cristinacolpos/PELA-blocks/motor/PELA-round-motor-enclosure.stl

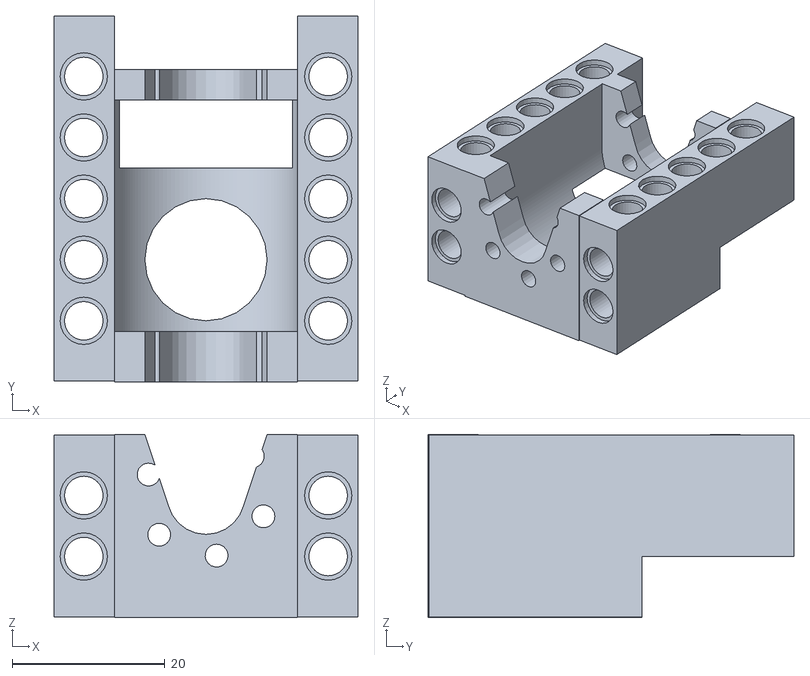
[picture p65: CAD file, 2020-01-09]
motor/PELA-round-motor-enclosure.stl
39.8 x 47.9 x 24.0
