cristinacolpos/PELA-blocks/peg/PELA-simplified-technic-peg-flexmaterial.stl

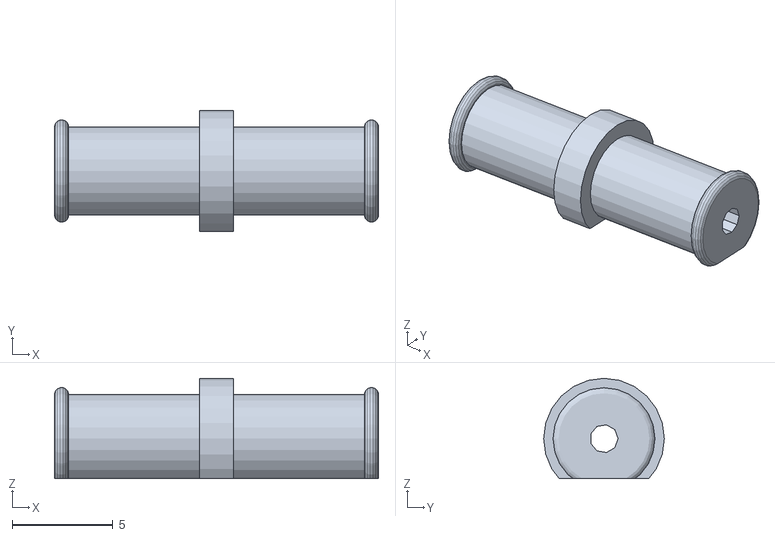
[picture p66: CAD file, 2020-01-09]
peg/PELA-simplified-technic-peg-flexmaterial.stl
16.1 x 6.00 x 4.99
