cristinacolpos/PELA-blocks/PELA-technic-block.stl

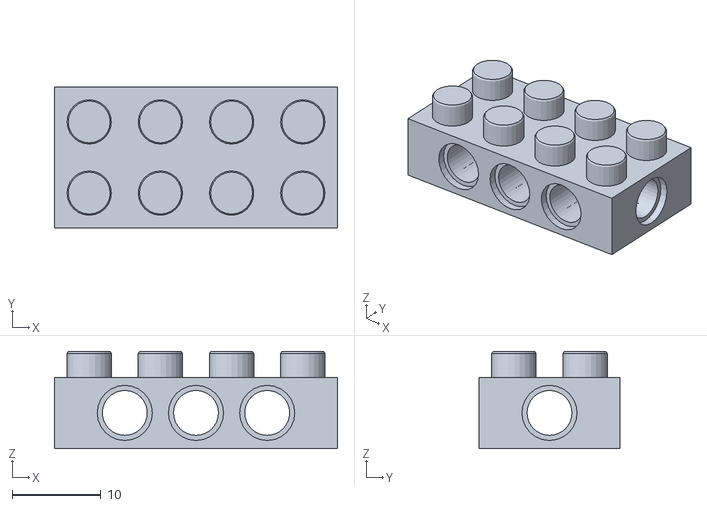
[picture p67: CAD file, 2020-01-09]
PELA-technic-block.stl
31.8 x 15.8 x 10.9
