cristinacolpos/PELA-blocks/sign/PELA-panel-sign.stl

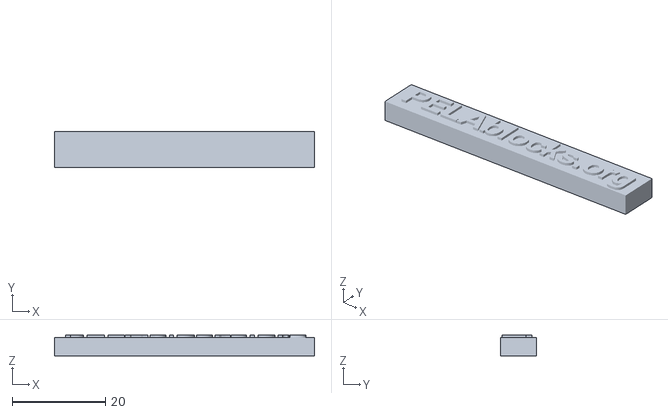
[picture p68: CAD file, 2019-11-25]
sign/PELA-panel-sign.stl
55.8 x 7.80 x 4.50
