cristinacolpos/PELA-blocks/technic-beam/PELA-technic-rail.stl

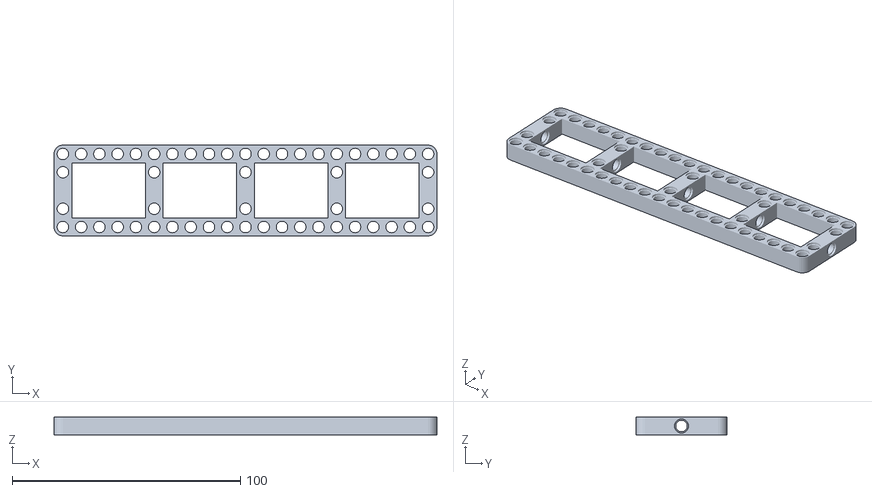
[picture p69: CAD file, 2020-01-09]
technic-beam/PELA-technic-rail.stl
167.8 x 39.8 x 7.80
