cristinacolpos/PELA-blocks/technic-mount/PELA-raspberry-pi-camera-technic-mount.stl

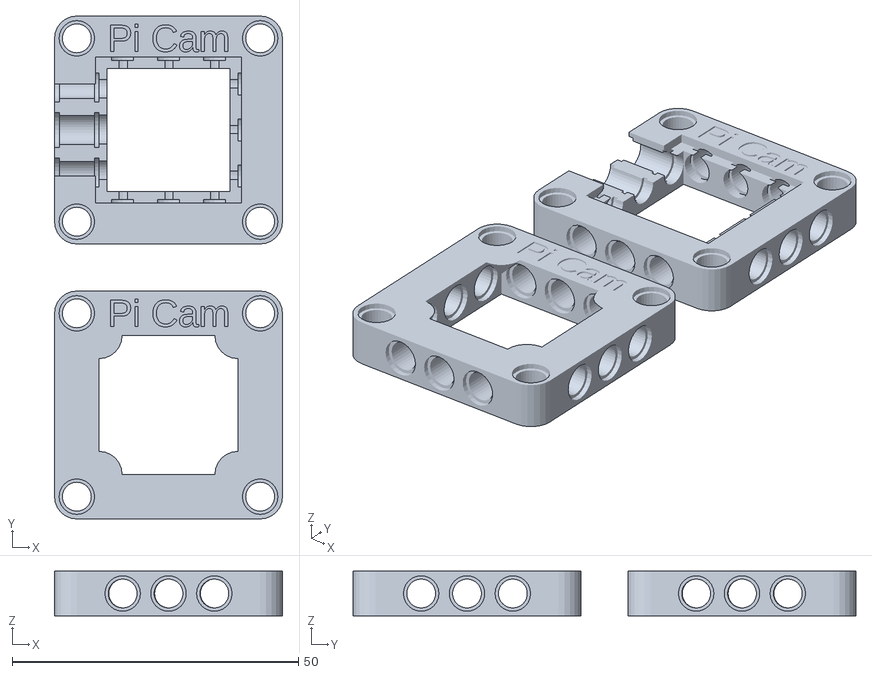
[picture p70: CAD file, 2020-01-09]
technic-mount/PELA-raspberry-pi-camera-technic-mount.stl
39.8 x 87.8 x 7.80
