cristinacolpos/PELA-blocks/axle/PELA-technic-axle.stl

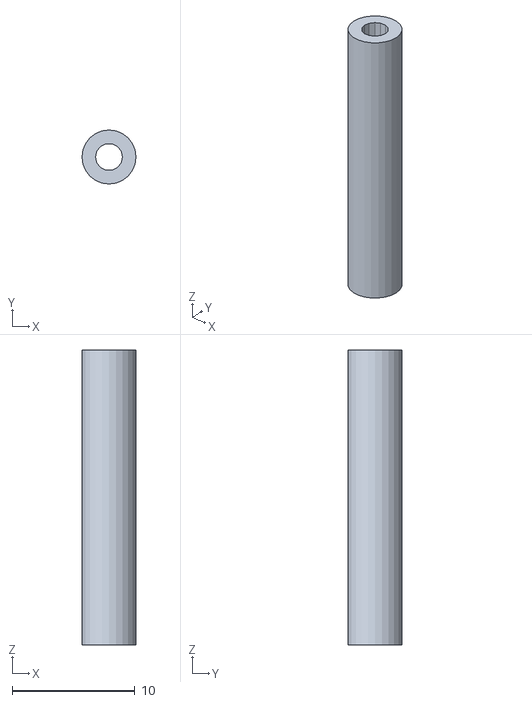
[picture p71: CAD file, 2019-11-25]
axle/PELA-technic-axle.stl
4.40 x 4.40 x 24.0
