cristinacolpos/PELA-blocks/peg/PELA-technic-peg.stl

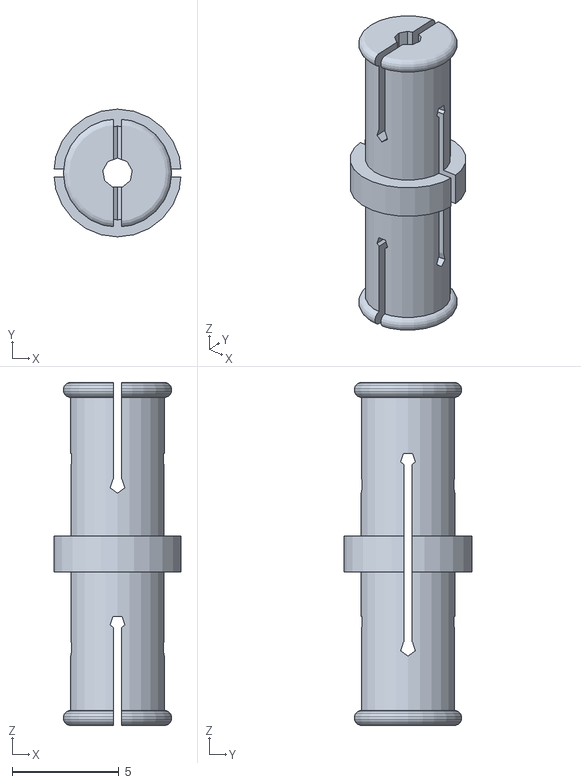
[picture p72: CAD file, 2020-01-09]
peg/PELA-technic-peg.stl
5.95 x 6.00 x 16.1
