cristinacolpos/PELA-blocks/PELA-strap-mount.stl

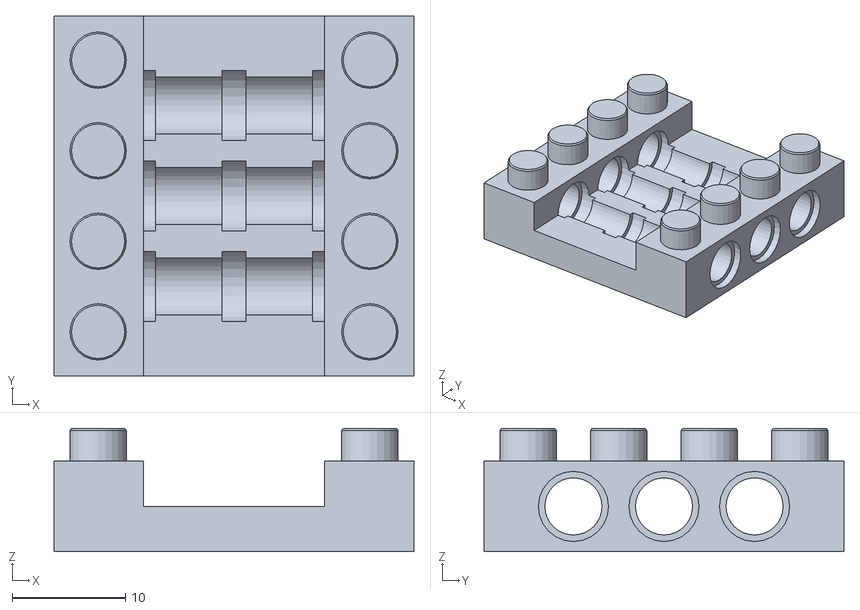
[picture p73: CAD file, 2020-01-09]
PELA-strap-mount.stl
31.8 x 31.8 x 10.9
