cristinacolpos/PELA-blocks/technic-beam/PELA-technic-twist-beam.stl

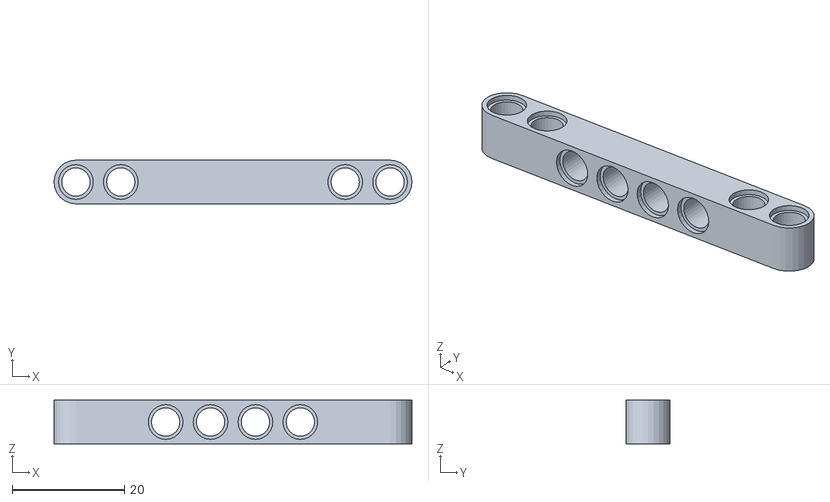
[picture p74: CAD file, 2020-01-09]
technic-beam/PELA-technic-twist-beam.stl
63.8 x 7.80 x 7.80
