cristinacolpos/PELA-blocks/technic-beam/PELA-technic-beam.stl

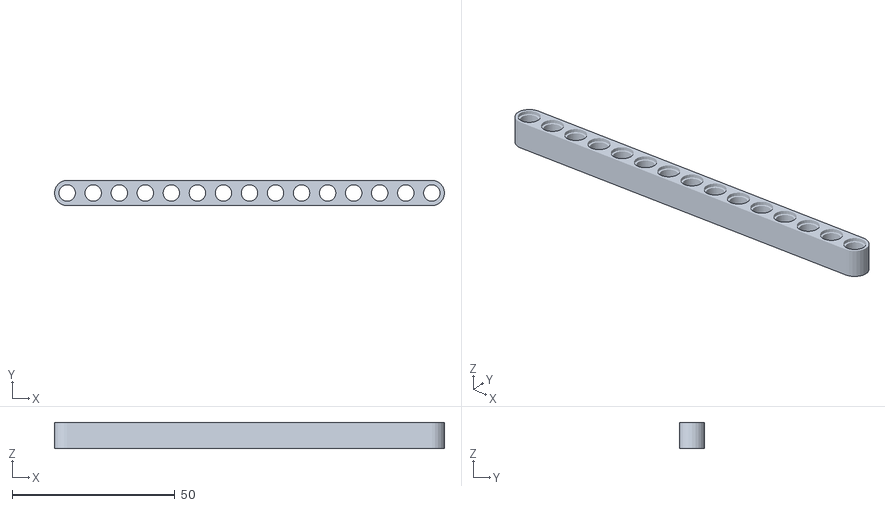
[picture p75: CAD file, 2020-01-09]
technic-beam/PELA-technic-beam.stl
119.8 x 7.80 x 8.00
