cristinacolpos/PELA-blocks/sign/PELA-sign.scad

/*
PELA Parametric Sign Generator

Create 2 symmetric end pieces which can support a solid object with PELA-compatible attachment points on top and bottom. By printing only the end pieces instead of a complele enclosure, the print is minimized



Based on
    https://www.thingiverse.com/thing:2303714



By Paul Houghton
Twitter: @mobile_rat
Email: paulirotta@gmail.com
Blog: https://medium.com/@paulhoughton

Creative Commons Attribution-ShareAlike 4.0 International License
    https://creativecommons.org/licenses/by-sa/4.0/legalcode

Open source design, Powered By Futurice. Come work with the best.
    https://www.futurice.com/

Import this into other design files:
    use <PELA-sign.scad>
    use <../PELA-block.scad>
    use <../PELA-technic-block.scad>
*/

include <../style.scad>
include <../print-parameters.scad>
use <../PELA-block.scad>
use <../PELA-technic-block.scad>

/* [PELA Sign Options] */

// Length of the sign (PELA knob count)
l = 9; 

// Width of the sign (PELA knob count)
w = 1;

// Height of the sign (PELA block layers)
h = 2;

// The top line of text. Set to "" to not have any top line
line_1 = "Rapid Prototyping";

// The second line of text
line_2 = "PELAblocks.org";

// 1=>text is pushing outward from the PELA block, 0=>etch text into the block
extrude = 1;

// Place the text on both sides
copy_to_back = true;

// Language of the text
lang = "en";

// The font to use for text on the top line
f1 = "Liberation Sans:style=Bold Italic";

// The font to use for text on the bottom line
f2 = "Arial";

// The font size (points) of the top line
fs1 = 5.8;

// The font size (points) of the bottom line
fs2 = 5;

// How deeply into the PELA block to etch/extrude the text
extrusion_height = 0.5;

// Left text margin (mm)
left_margin = 1.2;

// Top and bottom text margin (mm)
vertical_margin = 1;

// Width of a line etched in the side of multi-layer block sets (0 to disable, 0.15 on other types of blocks)
ridge_width = 0;

// Depth of a line etched in the side of multi-layer block sets (unused if ridge_width=0)
ridge_depth = 0.3;

// Add full width through holes spaced along the length for PELA Techics connectors
side_holes = 0; // [0:disabled, 1:short air vents, 2:short connectors, 3:full width connectors]

// Add a wrapper around Technic side holes (only used if there are side_holes, disable for extra ventilation, enable for connector lock notches)
side_sheaths = true;

// Add short end holes spaced along the width for PELA Techics connectors
end_holes = 2; // [0:disabled, 1:short air vents, 2:short connectors, 3:full length connectors]

// Add a wrapper around end holes  (only used if there are end_holes, disable for extra ventilation, enable for connector lock notches)
end_sheaths = true;

// Add holes in the top deck to improve airflow and reduce weight
top_vents = true;

// Place holes in the corners for mountings screws (0=>no holes, 1=>holes)
corner_bolt_holes = false;




///////////////////////////////
// DISPLAY
///////////////////////////////

PELA_sign();



///////////////////////////////////
// MODULES
///////////////////////////////////

module PELA_sign(l=l, w=w, h=h, line_1=line_1, line_2=line_2, lang=lang, extrude=extrude,  extrusion_height=extrusion_height, f1=f1, f2=f2, fs1=fs1, fs2=fs2, left_margin=left_margin, vertical_margin=vertical_margin, top_vents=top_vents, side_holes=side_holes, side_sheaths=side_sheaths, end_holes=end_holes, end_sheaths=end_sheaths, corner_bolt_holes=corner_bolt_holes) {
    
    if (extrude) {
        PELA_technic_block(l=l, w=w, h=h, ridge_width=ridge_width, ridge_depth=ridge_depth, top_vents=top_vents, side_holes=side_holes, side_sheaths=side_sheaths, end_holes=end_holes, end_sheaths=end_sheaths, corner_bolt_holes=corner_bolt_holes);
        
        translate([skin, skin, 0])
            PELA_sign_extruded_text(l=l, w=w, h=h, line_1=line_1, line_2=line_2, lang=lang, extrusion_height=extrusion_height, f1=f1, f2=f2, fs1=fs1, fs2=fs2, left_margin=left_margin, vertical_margin=vertical_margin);

        if (copy_to_back) {
            translate([block_width(l), block_width(w)-skin, 0])
                rotate([0, 0, 180])
                    PELA_sign_extruded_text(l=l, w=w, h=h, line_1=line_1, line_2=line_2, lang=lang, extrusion_height=extrusion_height, f1=f1, f2=f2, fs1=fs1, fs2=fs2, left_margin=left_margin, vertical_margin=vertical_margin);
        }
    } else {
        difference() {
            PELA_technic_block(l=l, w=w, h=h, ridge_width=ridge_width, ridge_depth=ridge_depth, top_vents=top_vents, side_holes=side_holes, side_sheaths=side_sheaths, end_holes=end_holes, end_sheaths=end_sheaths, corner_bolt_holes=corner_bolt_holes);
            
            union() {
                translate([skin, 0, 0])
                    PELA_sign_etched_text(l=l, w=w, h=h, line_1=line_1, line_2=line_2, lang=lang, extrusion_height=extrusion_height+skin, f1=f1, f2=f2, fs1=fs1, fs2=fs2, left_margin=left_margin, vertical_margin=vertical_margin);

                if (copy_to_back) {
                    translate([block_width(l)-skin, block_width(w)-skin, 0])
                        rotate([0, 0, 180])
                            PELA_sign_etched_text(l=l, w=w, h=h, line_1=line_1, line_2=line_2, lang=lang, extrusion_height=extrusion_height+skin, f1=f1, f2=f2, fs1=fs1, fs2=fs2, left_margin=left_margin, vertical_margin=vertical_margin);
                }
            }
        }
    }
}


// Two lines of text extruded out from the surface
module PELA_sign_extruded_text(l=l, w=w, h=h, line_1=line_1, line_2=line_2, lang=lang, extrusion_height=extrusion_height, f1=f1, f2=f2, fs1=fs1, fs2=fs2, left_margin=left_margin, vertical_margin=vertical_margin) {
    
    translate([left_margin, 0, block_height(h)-vertical_margin])
        PELA_text(text=line_1, lang=lang, font=f1, font_size=fs1, vertical_alignment="top");
    translate([left_margin, 0, vertical_margin])
        PELA_text(text=line_2, lang=lang, font=f2, font_size=fs2, vertical_alignment="bottom");
}


// Two lines of text etched into the surface
module PELA_sign_etched_text(l=l, w=w, h=h, line_1=line_1, line_2=line_2, lang=lang,  extrusion_height=extrusion_height, f1=f1, f2=f2, fs1=fs1, fs2=fs2, left_margin=left_margin, vertical_margin=vertical_margin) {
    
    translate([left_margin, extrusion_height, block_height(h)-vertical_margin])
        PELA_text(text=line_1, lang=lang, extrusion_height=extrusion_height, font=f1, font_size=fs1, vertical_alignment="top");
    
    translate([left_margin, extrusion_height, vertical_margin])
        PELA_text(text=line_2, lang=lang, extrusion_height=extrusion_height, font=f2, font_size=fs2, vertical_alignment="baseline");
}


// Text for the side of blocks
module PELA_text(text=line_1, lang=lang, extrusion_height=extrusion_height, font=f1, font_size=fs1, vertical_alignment="bottom") {
    rotate([90,0,0])
        linear_extrude(height=extrusion_height)
            text(text=text, language=lang, font=font, size=font_size, halign="left", valign=vertical_alignment);
}
