cristinacolpos/PELA-blocks/technic-bar/PELA-technic-twist-bar.scad

/*
PELA technic angle - 3D Printed LEGO-compatible 30 degree bend

Published at https://PELAblocks.org

By Paul Houghton
Twitter: @mobile_rat
Email: paulirotta@gmail.com
Blog: https://medium.com/@paulhoughton

Creative Commons Attribution ShareAlike NonCommercial License
    https://creativecommons.org/licenses/by-sa/4.0/legalcode

Design work kindly sponsored by
    https://www.futurice.com

All modules are setup for stateless functional-style reuse in other OpenSCAD files.
To this end, you can always pass in and override all parameters to create
a new effect. Doing this is not natural to OpenSCAD, so apologies for all
the boilerplate arguments which are passed in to each module or any errors
that may be hidden by the sensible default values. This is an evolving art.
*/

include <../material.scad>
include <../style.scad>
use <../PELA-block.scad>
use <../PELA-technic-block.scad>
use <PELA-technic-bar.scad>

/* [Technic Twist Bar] */

// Show the inside structure [mm]
cut_line = 0; // [0:1:100]

// Printing material (set to select calibrated knob, socket and axle hole fit)
material = 0; // [0:PLA, 1:ABS, 2:PET, 3:Biofila Silk, 4:Pro1, 5:NGEN, 6:NGEN FLEX, 7:Bridge Nylon, 8:TPU95, 9:TPU85/NinjaFlex]

// Is the printer nozzle >= 0.5mm? If so, some features are enlarged to make printing easier
large_nozzle = true;

// Left side length of upward facing connectors [blocks]
left = 2; // [1:20]

// Center length of sideways facing connectors [blocks]
center = 4; // [0:20]

// Right side length of upward facing connectors [blocks]
right = 2; // [1:20]



///////////////////////////////
// DISPLAY
///////////////////////////////

technic_twist_bar(material=material, large_nozzle=large_nozzle, cut_line=cut_line, left=left, center=center, right=right);



///////////////////////////////////
// MODULES
///////////////////////////////////

module technic_twist_bar(material=material, large_nozzle=large_nozzle, cut_line=cut_line, left=left, center=center, right=right) {
    assert(left > 0, "Left side of twist bar must be at least 1")
    assert(center >= 0, "Center of twist bar must be at least 0")
    assert(right > 0, "Right side of twist bar must be at least 1")

    if (center == 0) {
        technic_bar(material=material, large_nozzle=large_nozzle, cut_line=cut_line, l=left+right);
    } else {
        difference() {
            union() {
                left_square_end_bar(material=material, large_nozzle=large_nozzle, l=left);

                translate([block_width(left), 0, 0]) {
                    translate([0, block_width(0.5), block_width(0.5)]) {
                        rotate([90, 0, 0]) {
                            square_end_bar(material=material, large_nozzle=large_nozzle, l=center);
                        }
                    }

                    translate([block_width(center), 0, 0]) {
                        right_square_end_bar(material=material, large_nozzle=large_nozzle, l=right);
                    }
                }
            }

            translate([block_width(-0.5), block_width(-0.5), 0]) {
                cut_space(material=material, large_nozzle=large_nozzle, w=left+center+right, l=left+center+right, cut_line=cut_line, h=1, block_height=block_height, knob_height=knob_height);
            }
        }
    }
}


module square_end_bar(material=material, large_nozzle=large_nozzle, l=undef) {

    intersection() {
        translate([-block_width(1), 0, 0]) {
            technic_bar(material=material, large_nozzle=large_nozzle, l=l+2);
        }

       bar_space(material=material, large_nozzle=large_nozzle, l=l);
    }
}


module right_square_end_bar(material=material, large_nozzle=large_nozzle, l=undef) {

    intersection() {
        translate([-block_width(1), 0, 0]) {
            technic_bar(material=material, large_nozzle=large_nozzle, l=l+1);
        }

       bar_space(material=material, large_nozzle=large_nozzle, l=l);
    }
}


module left_square_end_bar(material=material, large_nozzle=large_nozzle, l=undef) {

    translate([block_width(l-1), 0, block_height()]) {
        rotate([0, 180, 0]) {
            right_square_end_bar(material=material, large_nozzle=large_nozzle, l=l);
        }
    }
}


module bar_space(material=material, large_nozzle=large_nozzle, l=undef) {

    translate([block_width(-0.5), block_width(-0.5), 0]) {
        skinned_block(material=material, large_nozzle=large_nozzle, l=l, w=1, h=1, skin=0, block_height=8);
    }
}
