cristinacolpos/PELA-blocks/vive-tracker/PELA-vive-tracker-screw.scad

/*
PELA HTC Vive Tracker Mount Screw

Published at https://PELAblocks.org

By Paul Houghton
Twitter: @mobile_rat
Email: paulirotta@gmail.com
Blog: https://medium.com/@paulhoughton

Creative Commons Attribution-ShareAlike 4.0 International License
    https://creativecommons.org/licenses/by-sa/4.0/legalcode

Open source design, Powered By Futurice. Come work with the best.
    https://www.futurice.com/

Import this into other design files:
    use <PELA-block.scad>
*/

include <../style.scad>
include <../print-parameters.scad>
use <../PELA-block.scad>
use <../PELA-technic-block.scad>
use <../threads/threads.scad>

/* [PELA Vive Tracker Screw Options] */

// Screwhole border
thumbscrew_border_d=11;

// Thumbscrew cut for finger tension
cut = 0.8;

// Thumbscrew turns per inch
tpi = 20;

// Thumbscrew head height
height=panel_height(0.5)-skin;

// Thumscrew diameter of shaft (inches)
dInch=1/4;

// Thumbscrew total height (inches)
hInch=1/4;



///////////////////////////////
// DISPLAY
///////////////////////////////

thumbscrew();



///////////////////////////////////
// MODULES
///////////////////////////////////

module thumbscrew() {    
    translate([0, 0, height])
        us_bolt_thread(dInch=dInch, hInch=hInch, tpi=tpi);

    thumbscrew_head(height=height);
}


module thumbscrew_head(height=height) {
    cylinder(d=thumbscrew_border_d/2, h=height);

    difference() {
        difference() {
            cylinder(d=thumbscrew_border_d-0.2, h=height);
            translate([-cut/2, 0])
                cube([cut, thumbscrew_border_d, cut]);
            
        }
        union() {
            for (i = [30:30:360]) {
                rotate([0, 0, i])
                    translate([-cut/2, 0])
                        cube([cut, thumbscrew_border_d, cut]);
            }
        }
    }
}
